Collector3/espressobin_case/files/f2-edition.jpg

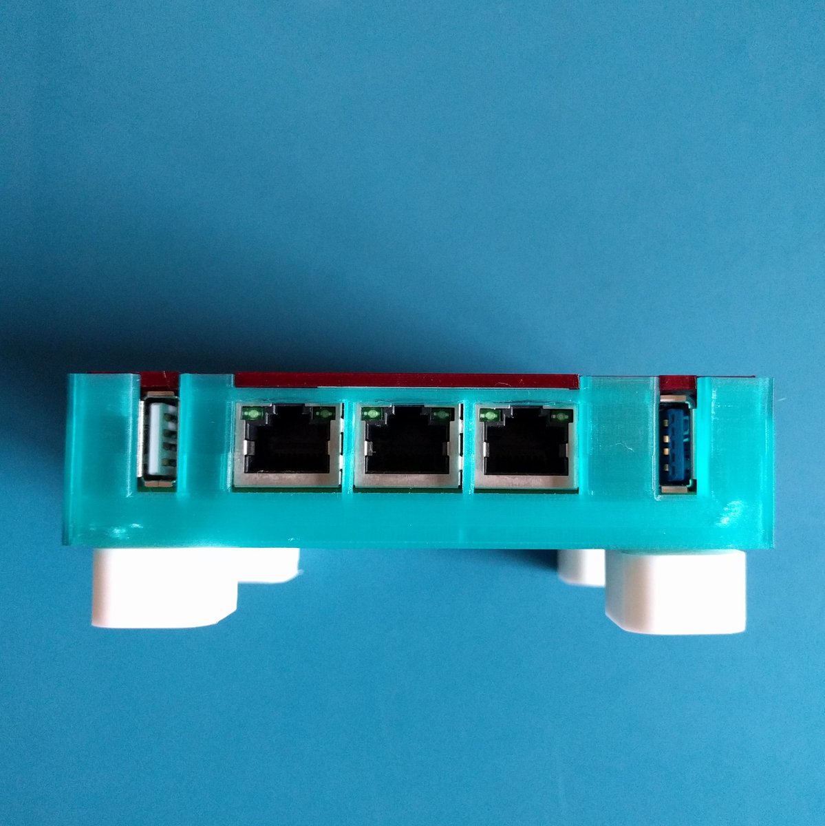
files/f2-edition.jpg
