Collector3/espressobin_case/images/528d6b0d0fbf60f37284c68c73a5a29c_preview_featured.jpg

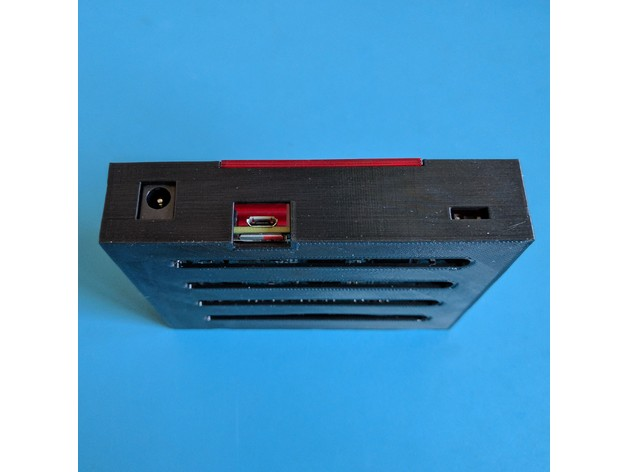
images/528d6b0d0fbf60f37284c68c73a5a29c_preview_featured.jpg
