Collector3/espressobin_case/images/51129e8a183095bf8f6e55a048500796_preview_featured.jpg

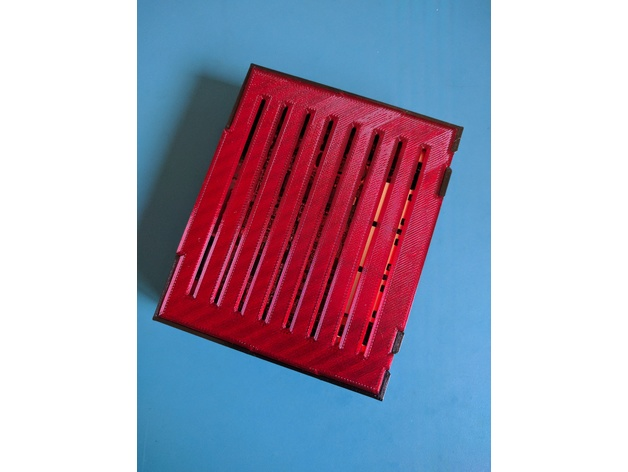
images/51129e8a183095bf8f6e55a048500796_preview_featured.jpg
