Collector3/espressobin_case/images/ba571a47812490d52d194f98f62db21e_preview_featured.jpg

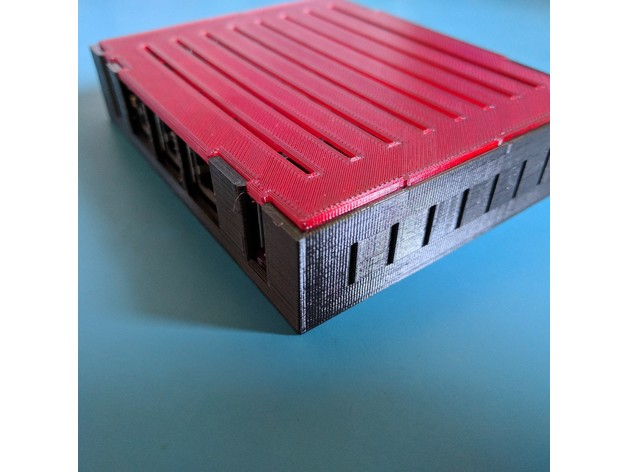
images/ba571a47812490d52d194f98f62db21e_preview_featured.jpg
