Collector3/espressobin_case/images/bottom.png

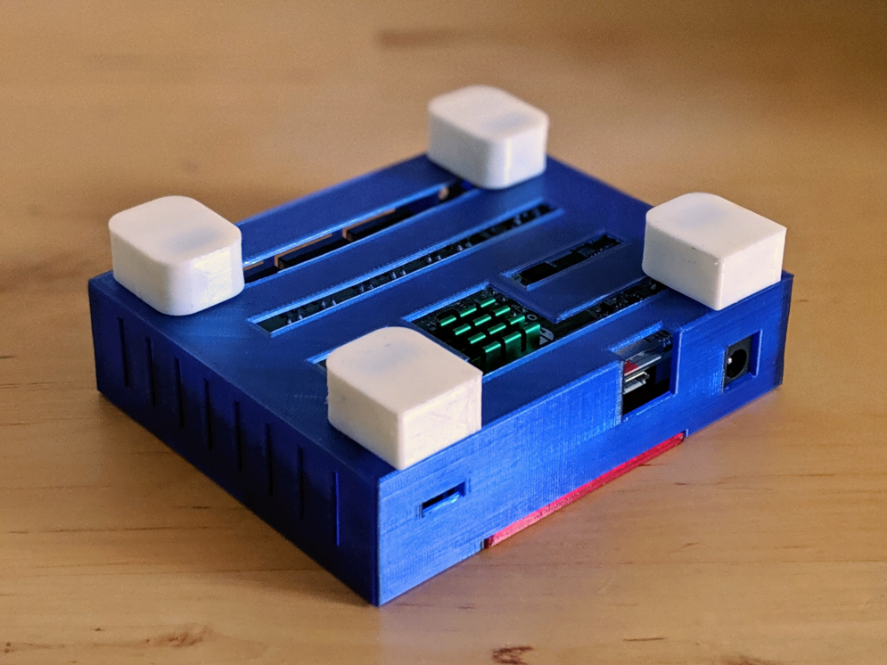
images/bottom.png
